norn93/NanoBot/Results/estimated_velocity_from_sampled_data.png

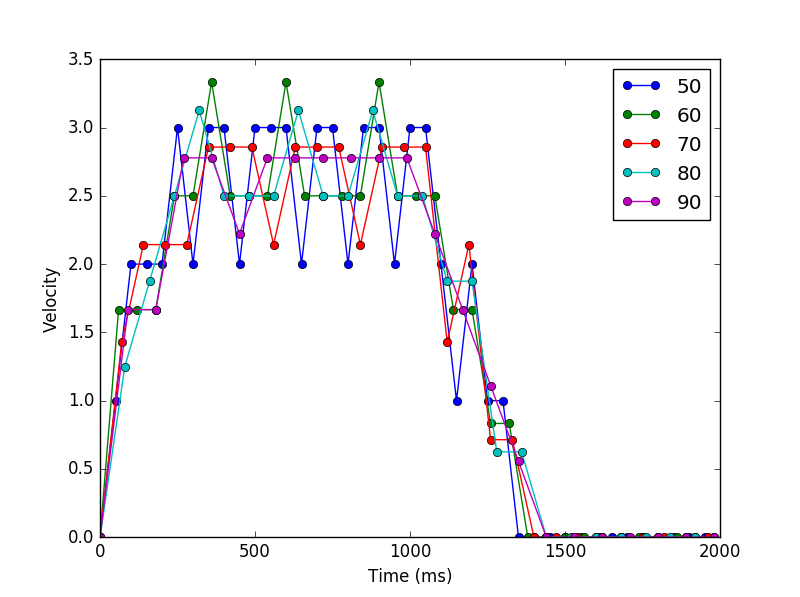
Results/estimated_velocity_from_sampled_data.png
