norn93/NanoBot/Results/time_data_from_file.png

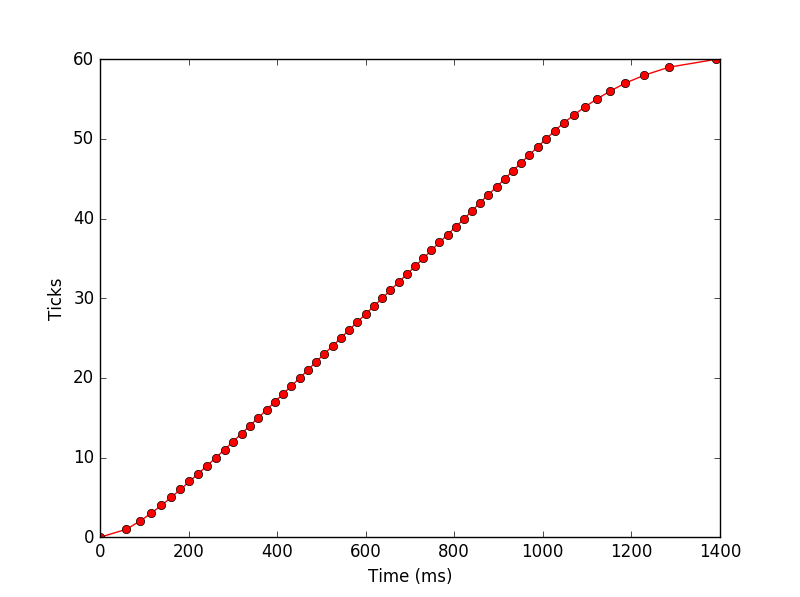
Results/time_data_from_file.png
